dukelec/cdbus_bridge/fw_bridge/usr/cd_config.h

/*
 * Software License Agreement (MIT License)
 *
 * Copyright (c) 2017, DUKELEC, Inc.
 * All rights reserved.
 *
 * Author: Duke Fong <d@d-l.io>
 */

#ifndef __CD_CONFIG_H__
#define __CD_CONFIG_H__

#define ARCH_SPI
#define CD_LIST_IT

#define DEBUG
//#define VERBOSE
#define DBG_STR_LEN         160
#define DBG_TX_IT
//#define LIST_DEBUG

#define CDUART_IRQ_SAFE
#define CDUART_IDLE_TIME    (500000 / SYSTICK_US_DIV) // 500 ms

#define CDN_SEQ
//#define CDN_L0_C
//#define CDN_L2

// un-comment this for 50Mbps version:
//#define CDCTL_SYS_CLK       150000000UL

#include "main.h"
#include "debug_config.h"

#endif
